Volcanite/2425_Maker_CashRegister/Software/STM32_Module_Paiement/Caisse_enregistreuse-teste/Core/Src/i2c.c

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
/* Includes ------------------------------------------------------------------*/
#include "i2c.h"

I2C_HandleTypeDef hi2c1;
I2C_HandleTypeDef hi2c2;

/* I2C1 init function */
void MX_I2C1_Init(void)
{

  /* USER CODE BEGIN I2C1_Init 1 */
	//BACKUP I2C config for RFID.
	/*hi2c1.Instance = I2C1;  // Utiliser I2C1 (par défaut sur PB6/PB7 pour Nucleo-L476RG)
	hi2c1.Init.Timing = 0x10805E89;  // Timing pour 100 kHz avec SYSCLK à 80 MHz (calculé via STM32CubeMX ou référence)
	hi2c1.Init.OwnAddress1 = 0;  // Pas d'adresse propre (mode maître)
	hi2c1.Init.AddressingMode = I2C_ADDRESSINGMODE_7BIT;  // Mode 7 bits pour PN532
	hi2c1.Init.DualAddressMode = I2C_DUALADDRESS_DISABLE;  // Désactiver mode double adresse
	hi2c1.Init.OwnAddress2 = 0;  // Pas d'adresse secondaire
	hi2c1.Init.OwnAddress2Masks = I2C_OA2_NOMASK;  // Pas de masque
	hi2c1.Init.GeneralCallMode = I2C_GENERALCALL_DISABLE;  // Désactiver appel général
	hi2c1.Init.NoStretchMode = I2C_NOSTRETCH_DISABLE;  // Activer mode stretch
	if (HAL_I2C_Init(&hi2c1) != HAL_OK)
	{
		Error_Handler();
	}*/
  /* USER CODE END I2C1_Init 1 */
  hi2c1.Instance = I2C1;
  hi2c1.Init.Timing = 0x10D19CE4;
  hi2c1.Init.OwnAddress1 = 0;
  hi2c1.Init.AddressingMode = I2C_ADDRESSINGMODE_7BIT;
  hi2c1.Init.DualAddressMode = I2C_DUALADDRESS_DISABLE;
  hi2c1.Init.OwnAddress2 = 0;
  hi2c1.Init.OwnAddress2Masks = I2C_OA2_NOMASK;
  hi2c1.Init.GeneralCallMode = I2C_GENERALCALL_DISABLE;
  hi2c1.Init.NoStretchMode = I2C_NOSTRETCH_DISABLE;
  if (HAL_I2C_Init(&hi2c1) != HAL_OK)
  {
    Error_Handler();
  }

  /** Configure Analogue filter
  */
  if (HAL_I2CEx_ConfigAnalogFilter(&hi2c1, I2C_ANALOGFILTER_ENABLE) != HAL_OK)
  {
    Error_Handler();
  }

  /** Configure Digital filter
  */
  if (HAL_I2CEx_ConfigDigitalFilter(&hi2c1, 0) != HAL_OK)
  {
    Error_Handler();
  }
}
/* I2C2 init function */
void MX_I2C2_Init(void)
{

  hi2c2.Instance = I2C2;
  hi2c2.Init.Timing = 0x00F12981;
  hi2c2.Init.OwnAddress1 = 0;
  hi2c2.Init.AddressingMode = I2C_ADDRESSINGMODE_7BIT;
  hi2c2.Init.DualAddressMode = I2C_DUALADDRESS_DISABLE;
  hi2c2.Init.OwnAddress2 = 0;
  hi2c2.Init.OwnAddress2Masks = I2C_OA2_NOMASK;
  hi2c2.Init.GeneralCallMode = I2C_GENERALCALL_DISABLE;
  hi2c2.Init.NoStretchMode = I2C_NOSTRETCH_DISABLE;
  if (HAL_I2C_Init(&hi2c2) != HAL_OK)
  {
    Error_Handler();
  }

  /** Configure Analogue filter
  */
  if (HAL_I2CEx_ConfigAnalogFilter(&hi2c2, I2C_ANALOGFILTER_ENABLE) != HAL_OK)
  {
    Error_Handler();
  }

  /** Configure Digital filter
  */
  if (HAL_I2CEx_ConfigDigitalFilter(&hi2c2, 0) != HAL_OK)
  {
    Error_Handler();
  }
}

void HAL_I2C_MspInit(I2C_HandleTypeDef* i2cHandle)
{

  GPIO_InitTypeDef GPIO_InitStruct = {0};
  RCC_PeriphCLKInitTypeDef PeriphClkInit = {0};
  if(i2cHandle->Instance==I2C1)
  {
  /** Initializes the peripherals clock
  */
    PeriphClkInit.PeriphClockSelection = RCC_PERIPHCLK_I2C1;
    PeriphClkInit.I2c1ClockSelection = RCC_I2C1CLKSOURCE_PCLK1;
    if (HAL_RCCEx_PeriphCLKConfig(&PeriphClkInit) != HAL_OK)
    {
      Error_Handler();
    }

    __HAL_RCC_GPIOB_CLK_ENABLE();
    /**I2C1 GPIO Configuration
    PB6     ------> I2C1_SCL
    PB9     ------> I2C1_SDA
    */
    GPIO_InitStruct.Pin = GPIO_PIN_6|GPIO_PIN_9;
    GPIO_InitStruct.Mode = GPIO_MODE_AF_OD;
    GPIO_InitStruct.Pull = GPIO_NOPULL;
    GPIO_InitStruct.Speed = GPIO_SPEED_FREQ_VERY_HIGH;
    GPIO_InitStruct.Alternate = GPIO_AF4_I2C1;
    HAL_GPIO_Init(GPIOB, &GPIO_InitStruct);

    /* I2C1 clock enable */
    __HAL_RCC_I2C1_CLK_ENABLE();
  }
  else if(i2cHandle->Instance==I2C2)
  {
  /** Initializes the peripherals clock
  */
    PeriphClkInit.PeriphClockSelection = RCC_PERIPHCLK_I2C2;
    PeriphClkInit.I2c2ClockSelection = RCC_I2C2CLKSOURCE_PCLK1;
    if (HAL_RCCEx_PeriphCLKConfig(&PeriphClkInit) != HAL_OK)
    {
      Error_Handler();
    }

    __HAL_RCC_GPIOB_CLK_ENABLE();
    /**I2C2 GPIO Configuration
    PB13     ------> I2C2_SCL
    PB14     ------> I2C2_SDA
    */
    GPIO_InitStruct.Pin = GPIO_PIN_13|GPIO_PIN_14;
    GPIO_InitStruct.Mode = GPIO_MODE_AF_OD;
    GPIO_InitStruct.Pull = GPIO_NOPULL;
    GPIO_InitStruct.Speed = GPIO_SPEED_FREQ_VERY_HIGH;
    GPIO_InitStruct.Alternate = GPIO_AF4_I2C2;
    HAL_GPIO_Init(GPIOB, &GPIO_InitStruct);

    /* I2C2 clock enable */
    __HAL_RCC_I2C2_CLK_ENABLE();
  }
}

void HAL_I2C_MspDeInit(I2C_HandleTypeDef* i2cHandle)
{

  if(i2cHandle->Instance==I2C1)
  {
    /* Peripheral clock disable */
    __HAL_RCC_I2C1_CLK_DISABLE();

    /**I2C1 GPIO Configuration
    PB6     ------> I2C1_SCL
    PB9     ------> I2C1_SDA
    */
    HAL_GPIO_DeInit(GPIOB, GPIO_PIN_6);

    HAL_GPIO_DeInit(GPIOB, GPIO_PIN_9);

  }
  else if(i2cHandle->Instance==I2C2)
  {
    /* Peripheral clock disable */
    __HAL_RCC_I2C2_CLK_DISABLE();

    /**I2C2 GPIO Configuration
    PB13     ------> I2C2_SCL
    PB14     ------> I2C2_SDA
    */
    HAL_GPIO_DeInit(GPIOB, GPIO_PIN_13);

    HAL_GPIO_DeInit(GPIOB, GPIO_PIN_14);

  }
}
