Volcanite/2425_Maker_CashRegister/Software/STM32_Module_Paiement/Caisse_enregistreuse-teste/Core/Src/Screen.c

/*
 * Screen.c
 *
 *  Created on: Oct 27, 2025
 *      Author: garbe
 */

#include "Screen.h"

const unsigned char logo_battery_25[]= {
		0x3F, 0xFF, 0xFF, 0xFF, 0xFF, 0xFF, 0xFF, 0x80,
		0x7F, 0xFF, 0xFF, 0xFF, 0xFF, 0xFF, 0xFF, 0xC0,
		0xE0, 0x00, 0x00, 0x00, 0x00, 0x00, 0x00, 0xE0,
		0xC0, 0x00, 0x00, 0x00, 0x00, 0x00, 0x00, 0x60,
		0xC0, 0x00, 0x00, 0x00, 0x00, 0x00, 0x00, 0x60,
		0xC3, 0xFE, 0x00, 0x00, 0x00, 0x00, 0x00, 0x60,
		0xC3, 0xFE, 0x00, 0x00, 0x00, 0x00, 0x00, 0x60,
		0xC3, 0xFE, 0x00, 0x00, 0x00, 0x00, 0x00, 0x60,
		0xC3, 0xFE, 0x00, 0x00, 0x00, 0x00, 0x00, 0x78,
		0xC3, 0xFE, 0x00, 0x00, 0x00, 0x00, 0x00, 0x7F,
		0xC3, 0xFE, 0x00, 0x00, 0x00, 0x00, 0x00, 0x7F,
		0xC3, 0xFE, 0x00, 0x00, 0x00, 0x00, 0x00, 0x63,
		0xC3, 0xFE, 0x00, 0x00, 0x00, 0x00, 0x00, 0x63,
		0xC3, 0xFE, 0x00, 0x00, 0x00, 0x00, 0x00, 0x63,
		0xC3, 0xFE, 0x00, 0x00, 0x00, 0x00, 0x00, 0x63,
		0xC3, 0xFE, 0x00, 0x00, 0x00, 0x00, 0x00, 0x63,
		0xC3, 0xFE, 0x00, 0x00, 0x00, 0x00, 0x00, 0x63,
		0xC3, 0xFE, 0x00, 0x00, 0x00, 0x00, 0x00, 0x63,
		0xC3, 0xFE, 0x00, 0x00, 0x00, 0x00, 0x00, 0x63,
		0xC3, 0xFE, 0x00, 0x00, 0x00, 0x00, 0x00, 0x63,
		0xC3, 0xFE, 0x00, 0x00, 0x00, 0x00, 0x00, 0x63,
		0xC3, 0xFE, 0x00, 0x00, 0x00, 0x00, 0x00, 0x7F,
		0xC3, 0xFE, 0x00, 0x00, 0x00, 0x00, 0x00, 0x7E,
		0xC3, 0xFE, 0x00, 0x00, 0x00, 0x00, 0x00, 0x70,
		0xC3, 0xFE, 0x00, 0x00, 0x00, 0x00, 0x00, 0x60,
		0xC3, 0xFE, 0x00, 0x00, 0x00, 0x00, 0x00, 0x60,
		0xC3, 0xFC, 0x00, 0x00, 0x00, 0x00, 0x00, 0x60,
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
	int minute = 00;

	char time_str[6];
	sprintf(time_str, "%02d:%02d", heure, minute);

	SSD1306_GotoXY(50, 50);  // Position X, Y
	SSD1306_Puts(time_str, &Font_7x10, 1);
	SSD1306_UpdateScreen(); // update screen<p style="margin:0;"></p>  while (1) { }
	return 1;
};

int Get_hour();
