Volcanite/2425_Maker_CashRegister/Software/STM32_Module_Paiement/Caisse_enregistreuse-teste/Core/Inc/RFID_Card_ReWr.h

/*
 * RFID_Card_ReWr.h
 *
 *  Created on: Oct 20, 2025
 *      Author: garbe
 */

#ifndef INC_RFID_CARD_REWR_H_
#define INC_RFID_CARD_REWR_H_

#include "main.h"
#include <stdio.h>
int RFID_init();
int RFID_Get_UID_Card();
int RFID_Get_Block_Information();

#endif /* INC_RFID_CARD_REWR_H_ */
