Volcanite/2425_Maker_CashRegister/Software/STM32_Module_Paiement/Caisse_enregistreuse-teste/Core/Inc/Screen.h

/*
 * Screen.h
 *
 *  Created on: Oct 27, 2025
 *      Author: garbe
 */

#ifndef INC_SCREEN_H_
#define INC_SCREEN_H_

#include "ssd1306.h"
#include "main.h"
#include "stdio.h"

int Initialisation();
int Default_Use();


#endif /* INC_SCREEN_H_ */
