Volcanite/2425_Maker_CashRegister/Software/STM32_Module_Paiement/Caisse_enregistreuse-teste/Core/Inc/bt.h

/*
 *  bt.h
 *
 *  Created on: April 23, 2025
 *      Author: garbez
 */

#ifndef INC_BT_H_
#define INC_BT_H_

#include "usart.h"
#include "main.h"
#include <string.h>
#include <stdint.h>
#include "stdio.h"
#include "string.h"

void bt_received ();


#endif /* INC_BT_H_ */
